b-karl/KBIC65/img/state_of_the_pcb_20210124.png

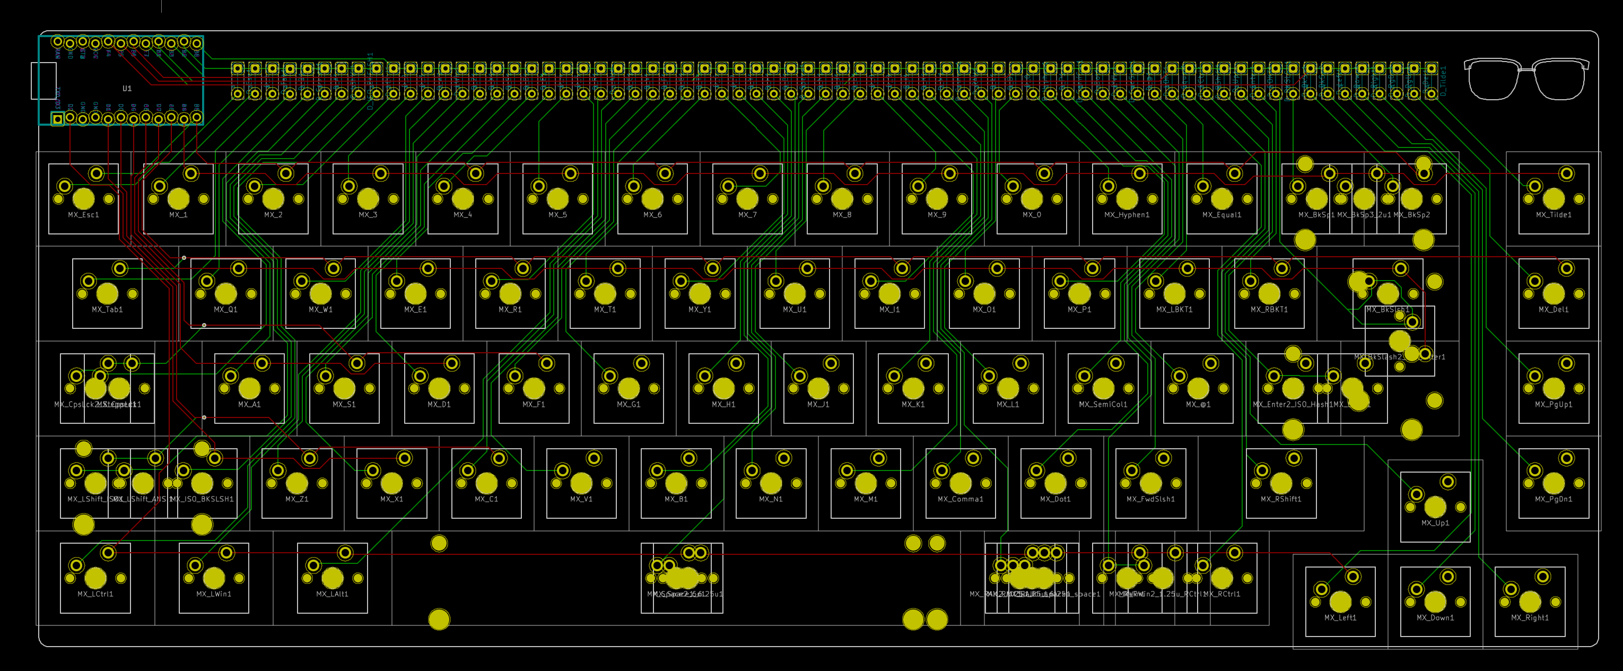
img/state_of_the_pcb_20210124.png
