b-karl/KBIC65/img/state_of_the_pcb_20210216.png

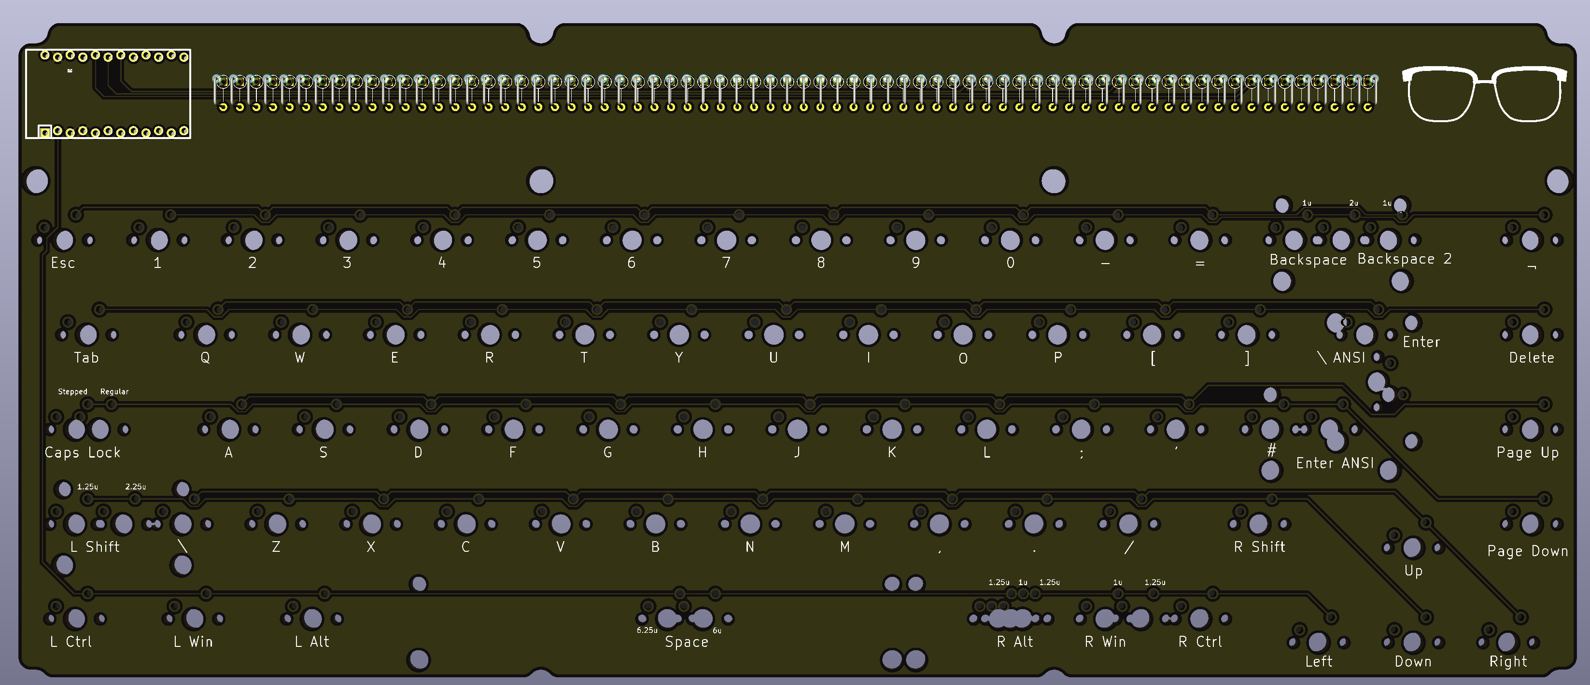
img/state_of_the_pcb_20210216.png
