b-karl/KBIC65/img/state_of_the_pcb_20210221_cad.png

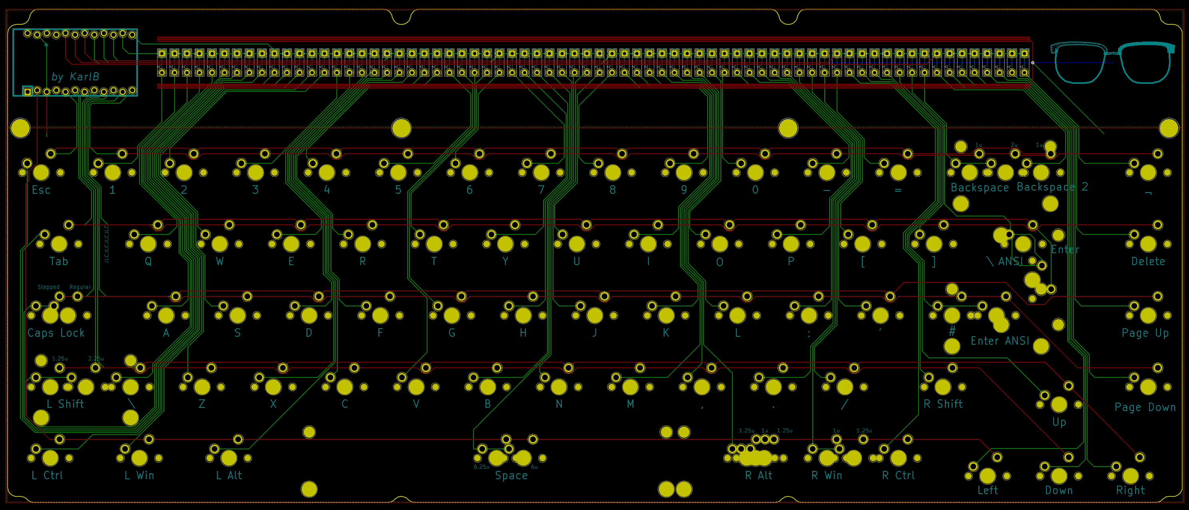
img/state_of_the_pcb_20210221_cad.png
