b-karl/KBIC65/img/build_log/20210331_194123.jpg

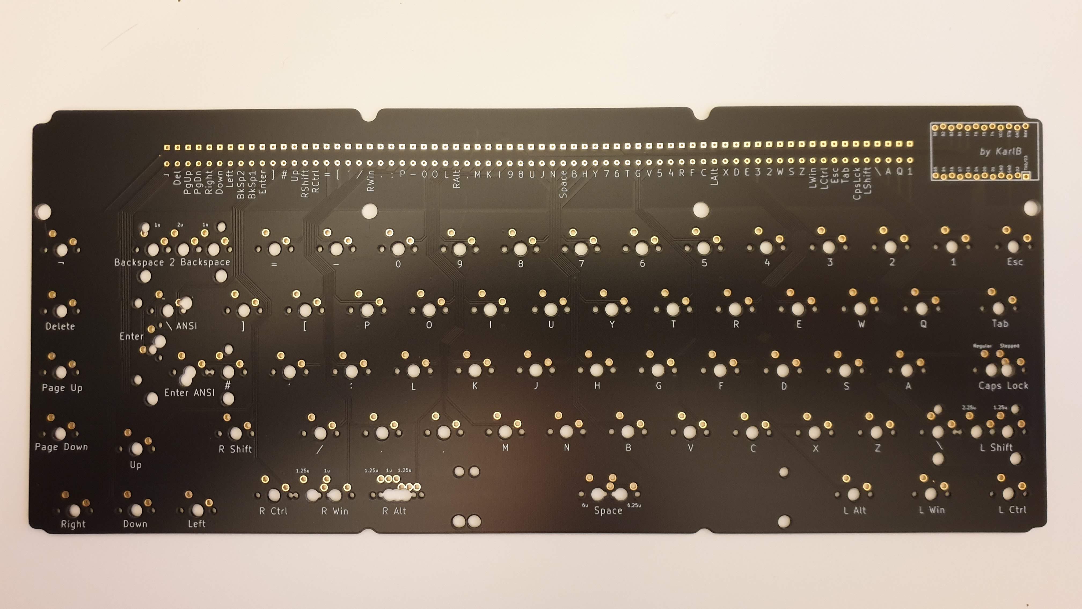
img/build_log/20210331_194123.jpg
