b-karl/KBIC65/img/build_log/20210405_201629.jpg

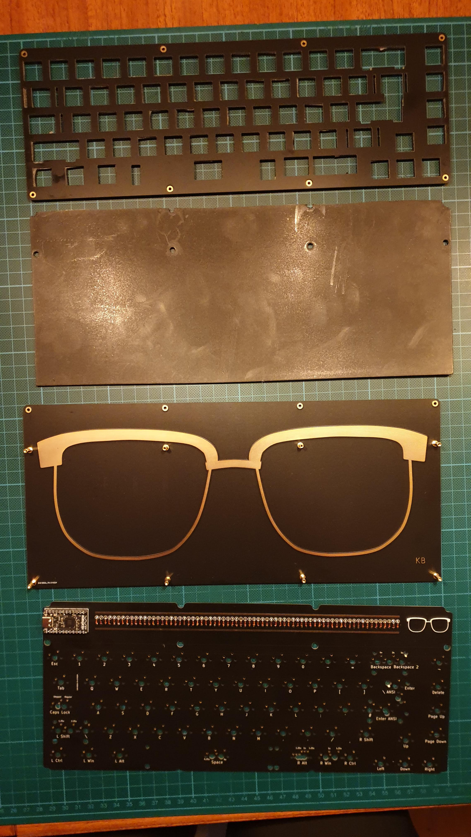
img/build_log/20210405_201629.jpg
